DIYsciBorg/Joule-Thief-Torch/images/2026-04-07 20.57.46.jpg

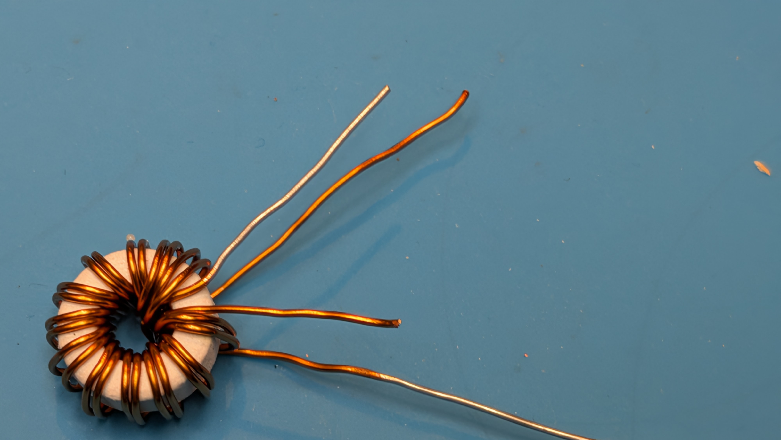
images/2026-04-07 20.57.46.jpg
