DIYsciBorg/Joule-Thief-Torch/images/JT coil 3.jpg

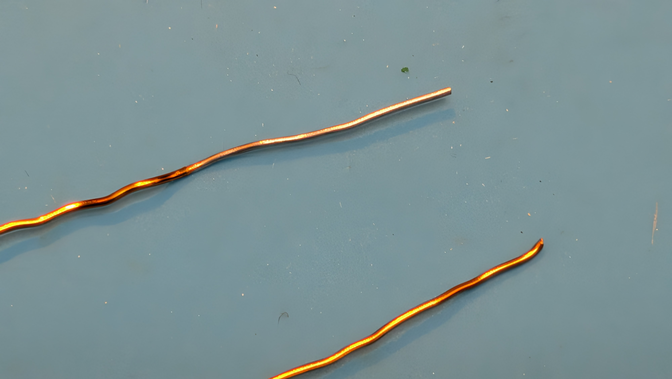
images/JT coil 3.jpg
