DIYsciBorg/Joule-Thief-Torch/images/JT pcb bottom.png

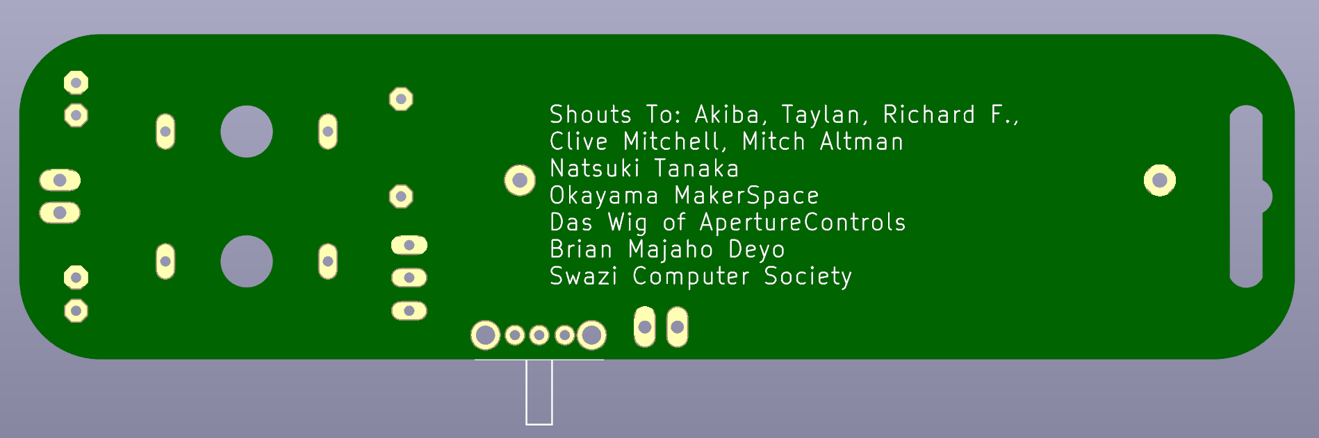
images/JT pcb bottom.png
