DIYsciBorg/Joule-Thief-Torch/images/JT pcb kicad.png

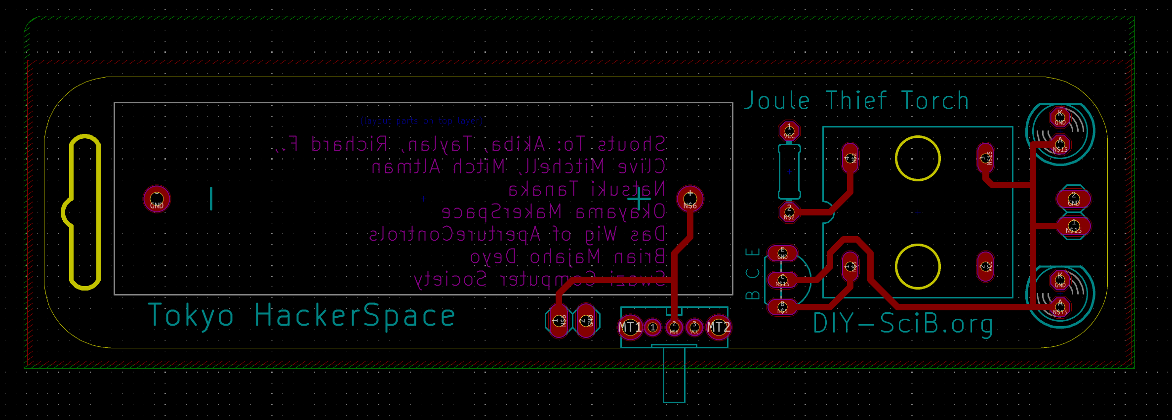
images/JT pcb kicad.png
