DIYsciBorg/Joule-Thief-Torch/images/JT pcb top.png

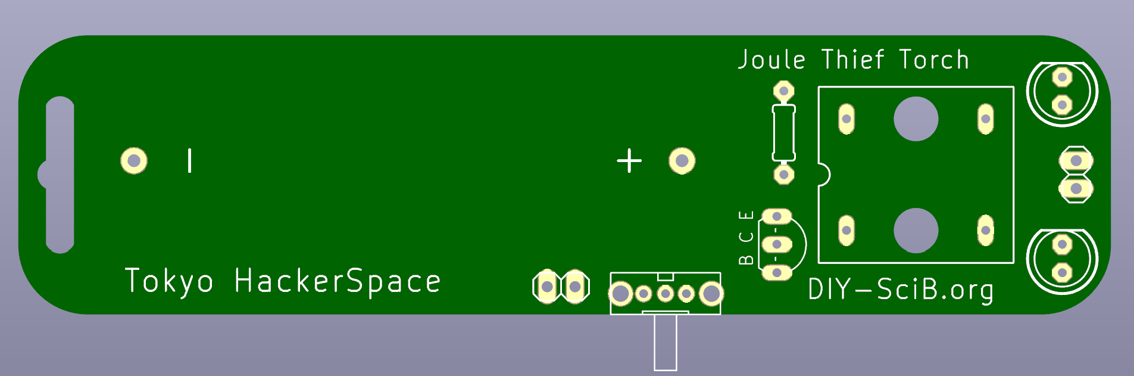
images/JT pcb top.png
